nicoMgrt/Proyecto-Sima-sistema-inteligente-en-monitoreo-del-aforo-Tei201/hardware/fotos/02_circuito_interno.jpeg

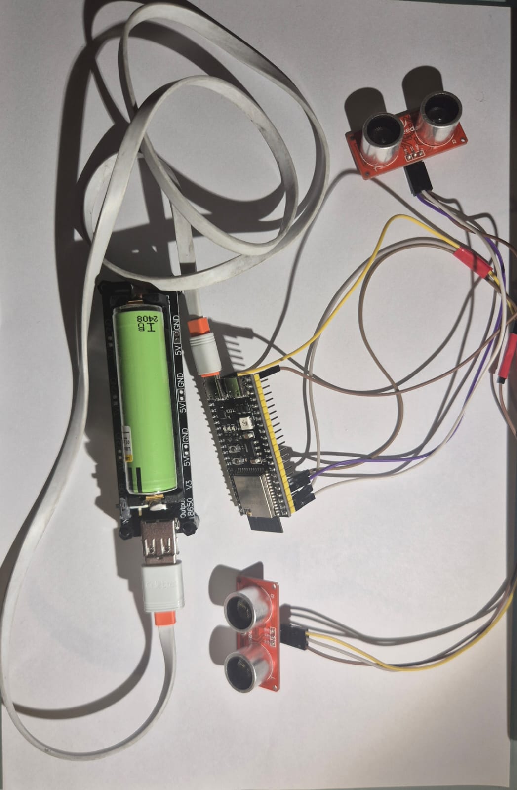
hardware/fotos/02_circuito_interno.jpeg
