nicoMgrt/Proyecto-Sima-sistema-inteligente-en-monitoreo-del-aforo-Tei201/hardware/fotos/04_sensores.jpeg

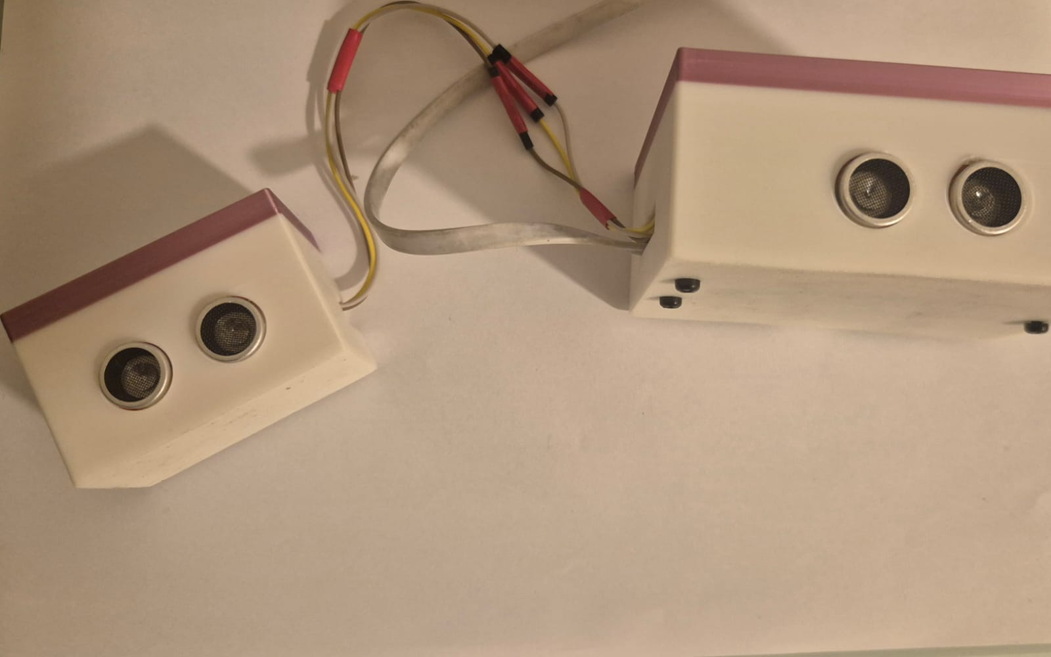
hardware/fotos/04_sensores.jpeg
