nicoMgrt/Proyecto-Sima-sistema-inteligente-en-monitoreo-del-aforo-Tei201/hardware/fotos/06_encapsulado_cerrado.jpeg

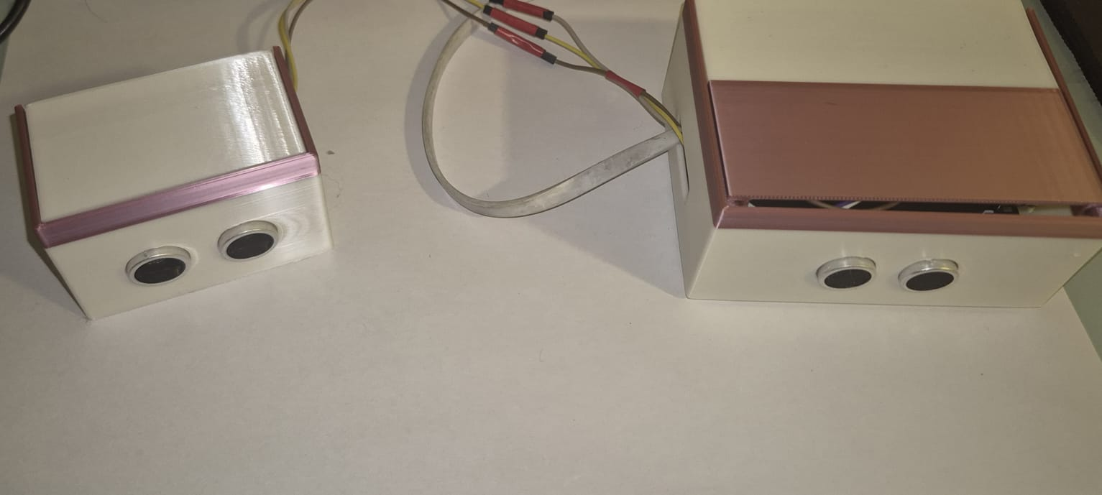
hardware/fotos/06_encapsulado_cerrado.jpeg
