nicoMgrt/Proyecto-Sima-sistema-inteligente-en-monitoreo-del-aforo-Tei201/software/docs/Diagrama de flujo 1.drawio.png

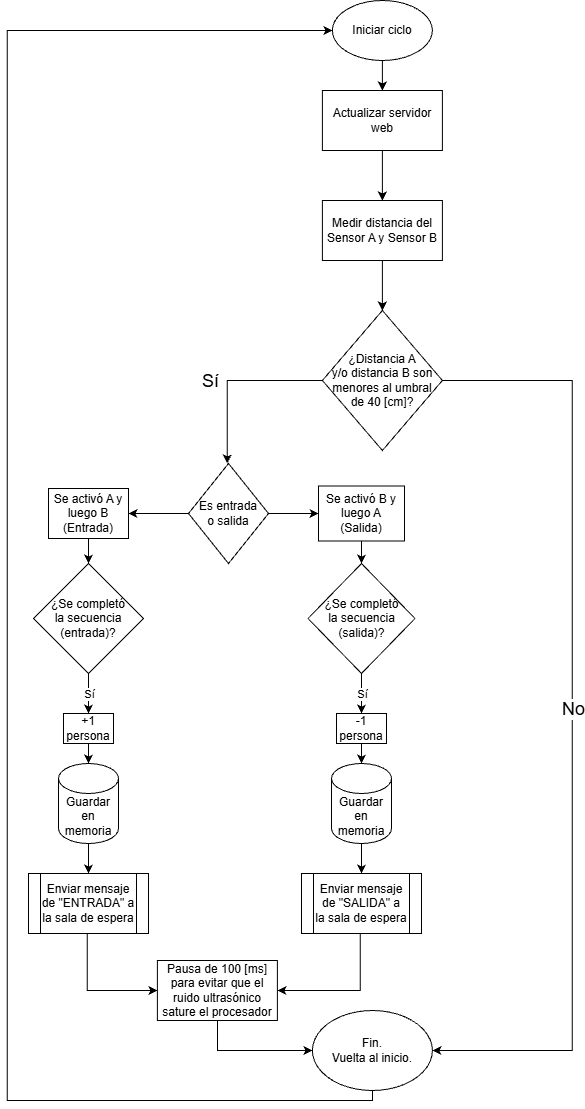
software/docs/Diagrama de flujo 1.drawio.png
