nicoMgrt/Proyecto-Sima-sistema-inteligente-en-monitoreo-del-aforo-Tei201/testing/evidencias/prototipo_lateral_01.jpg.jpeg

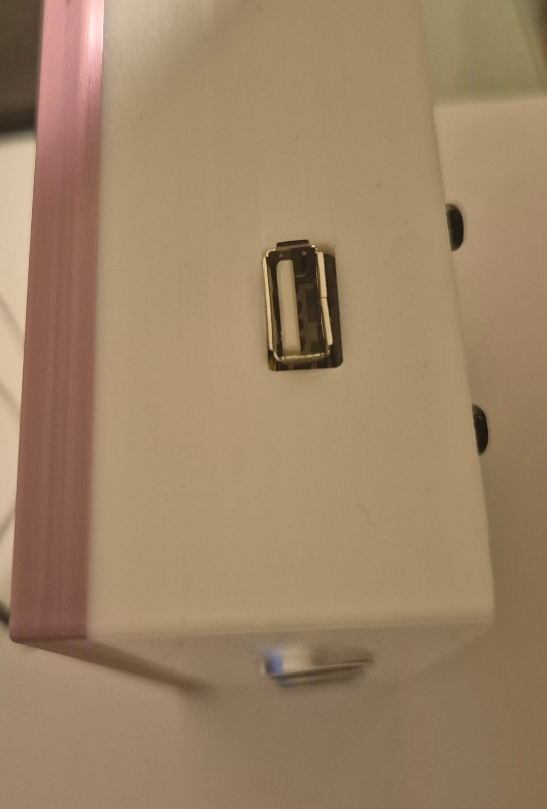
testing/evidencias/prototipo_lateral_01.jpg.jpeg
